mynthan3107/STEM/circuit/low pass first order.asc

C1: cap; 0.47µ
R1: res; 677.2
R2: res
R3: res
U1: TL074
Named nets: 0
vin
vout
Fist order low pass filter
fc=1/2piRc
gain=1+R2/R3
fc=500Hz
C=0.47uF
Rc=677.2ohm
