mynthan3107/STEM/circuit/power_supply.asc

C1: cap; 1000
C2: cap; 100n
C3: cap; 1000
C4: cap; 100n
D1: diode; 1N4007
D2: diode; 1N4007
D3: diode; 1N4007
D4: diode; 1N4007
L1: ind2; 132
L2: ind2; 1
L3: ind2; 1
R2: res; 1k
V4: voltage; SINE(0 325.26919 50)
Named nets: 0, +Vss, -Vss
Power Supply
K L1 L2 L3 1
7815 and 7915 Regulator IC for +/- and ground power supply
