mynthan3107/STEM/circuit/complete.asc

C1: cap; 100
C1: cap; 1000
C2: cap; 100
C2: cap; 100n
C3: cap; 0.47
C3: cap; 1000
C4: cap; 0.47
C4: cap; 100n
C8: cap; 0.47
C9: cap; 0.47
C10: cap; 0.47
C11: cap; 0.47
C12: cap; 1
D1: diode; 1N4007
D2: diode; 1N4007
D3: diode; 1N4007
D4: diode; 1N4007
L1: ind2; 132
L2: ind2; 1
L3: ind2; 1
R1: res; 159.2
R2: res; 1k
R2: res; 1000
R3: res; 159.2
R4: res; 1000
R5: res; 677.2
R6: res; 677.2
R7: res; 1000
R8: res; 1000
R9: res; 1000
R10: res; 1000
R11: res; 677.2
R12: res; 25k
R13: res; 10k
R14: res; 25k
R15: res; 10K
R16: res; 10k
R17: res; 10k
R18: res; 10k
R19: res; 1000k
R20: res; 1000k
R23: res; 677.2
R24: res; 6.8k
R25: res; 6.8k
U1: AD8032
U2: AD8032
U3: AD8032
U4: AD8032
U5: AD8032
U6: AD8032
V1: voltage; PWL file=C:\Users\thamilezai\Desktop\Analogue_sem_3\STEM\sample_signals\emgvalues_1.csv; AC 1
V2: voltage; PWL file=C:\Users\thamilezai\Desktop\Analogue_sem_3\STEM\sample_signals\emgvalues_2.csv; AC 2
V3: voltage; 15
V4: voltage; SINE(0 325.26919 50)
V5: voltage; 15
Named nets: 0, +Vss, -Vss
;tran 1
.ac dec 100 5 1000
Power Supply
K L1 L2 L3 1
7815 and 7915 Regulator IC for +/- and ground power supply
