mynthan3107/STEM/circuit/notch.asc

C1: cap; 0.47µ
C2: cap; 0.47µ
C3: cap; 1µ
R1: res; 6.8k
R2: res; 6.8k
Named nets: 0
