mynthan3107/STEM/circuit/high pass.asc

C1: cap
C2: cap
R1: res
R2: res
R3: res
R4: res
U1: TL074
Named nets: 0
