mynthan3107/STEM/circuit/low pass.asc

C1: cap; 0.47µ
C2: cap; 0.47µ
R1: res; 677.2
R2: res; 677.2
R3: res
R4: res
U1: TL074
Named nets: 0
vin
Second order Low pass   
gain= R3/R4
fc=1/2pi(R1 R2 C1 C2)^1/2
fc=500Hz
C1=C2=0.47uF
R1=R2=677.2 ohm
