mynthan3107/STEM/circuit/instrumental amplifier.asc

R1: res; 25k
R2: res; 10k
R3: res; 25k
R4: res; 10K
R5: res; 10k
R6: res; 10k
R7: res; 10k
U2: TL074
U3: TL074
U4: TL074
Named nets: 0
